TinyCircuits/TinyCircuits-TinyShield-Sensor-ASD2511/cad/TinyShield_SENSOR_BOARD_ASD2511_REV5-DETAILED_DRAWING_COMPACT-PNG.png

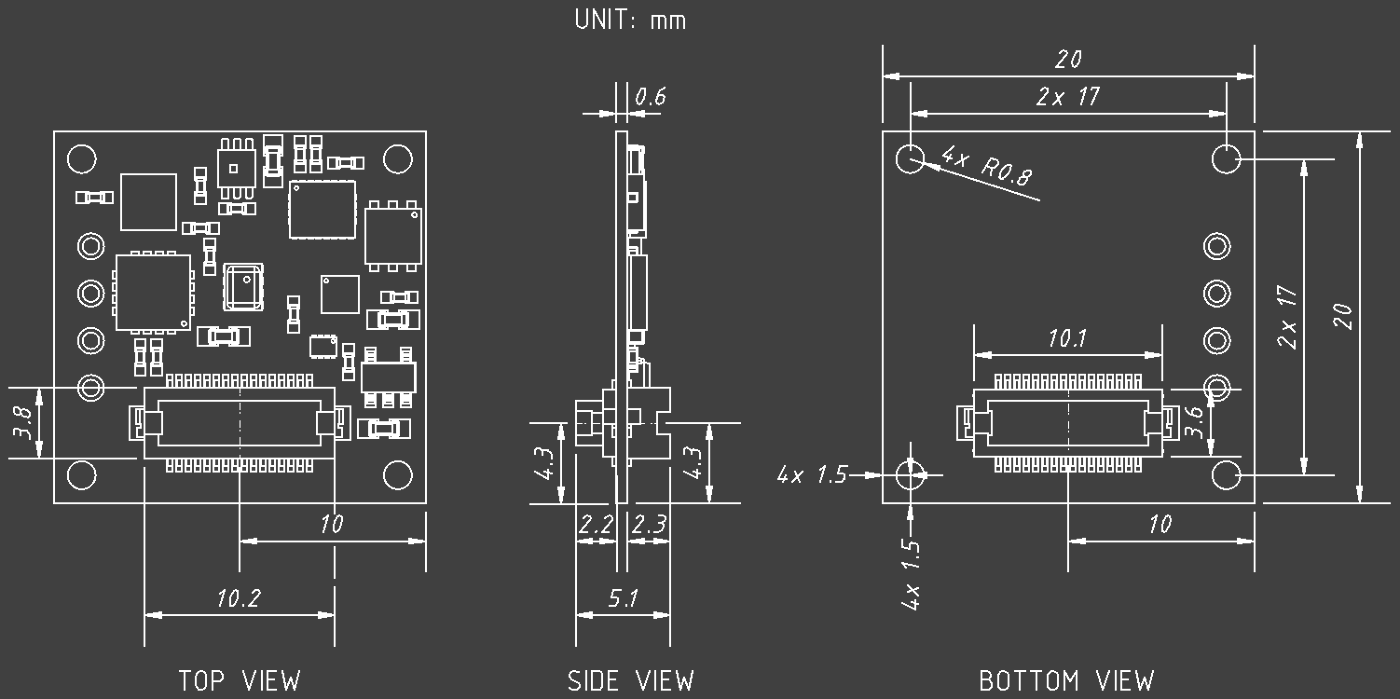
cad/TinyShield_SENSOR_BOARD_ASD2511_REV5-DETAILED_DRAWING_COMPACT-PNG.png
