TinyCircuits/TinyCircuits-TinyShield-Sensor-ASD2511/tutorial_images/ASD2511-R-P_Parts.JPG

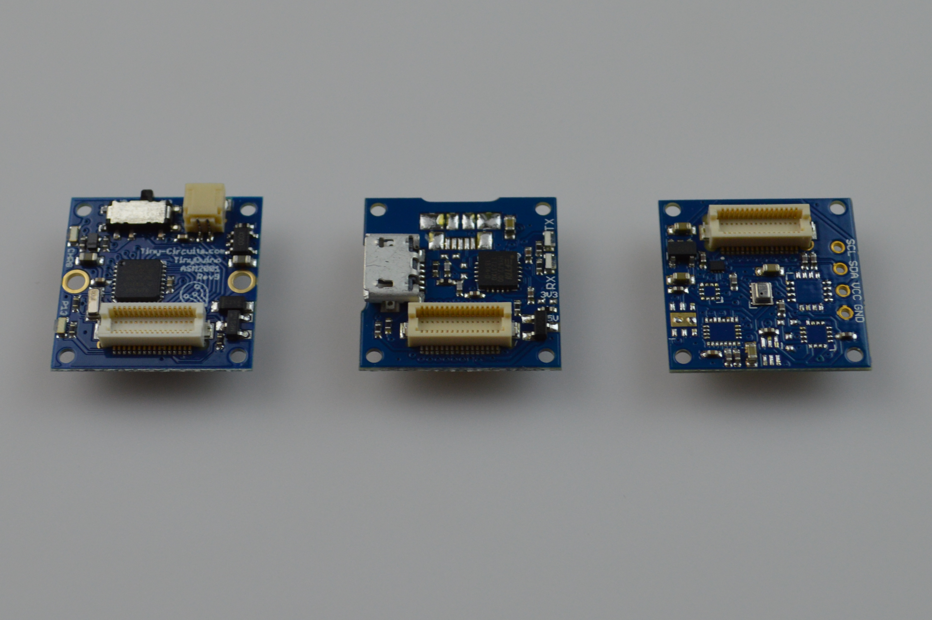
tutorial_images/ASD2511-R-P_Parts.JPG
