TinyCircuits/TinyCircuits-TinyShield-Sensor-ASD2511/images/tutorial_images_9-axis/ASD2511-R-N-Tutorial-Image-05.png

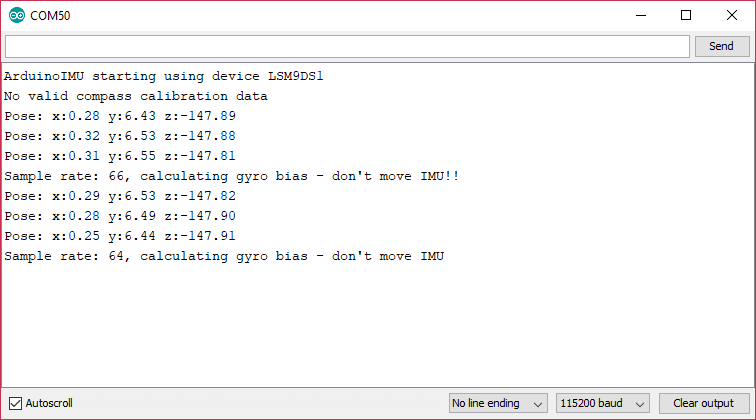
images/tutorial_images_9-axis/ASD2511-R-N-Tutorial-Image-05.png
