TinyCircuits/TinyCircuits-TinyShield-Sensor-ASD2511/images/tutorial_images_accelerometer/ASD2511-R-A-Tutorial-Image-03.jpg

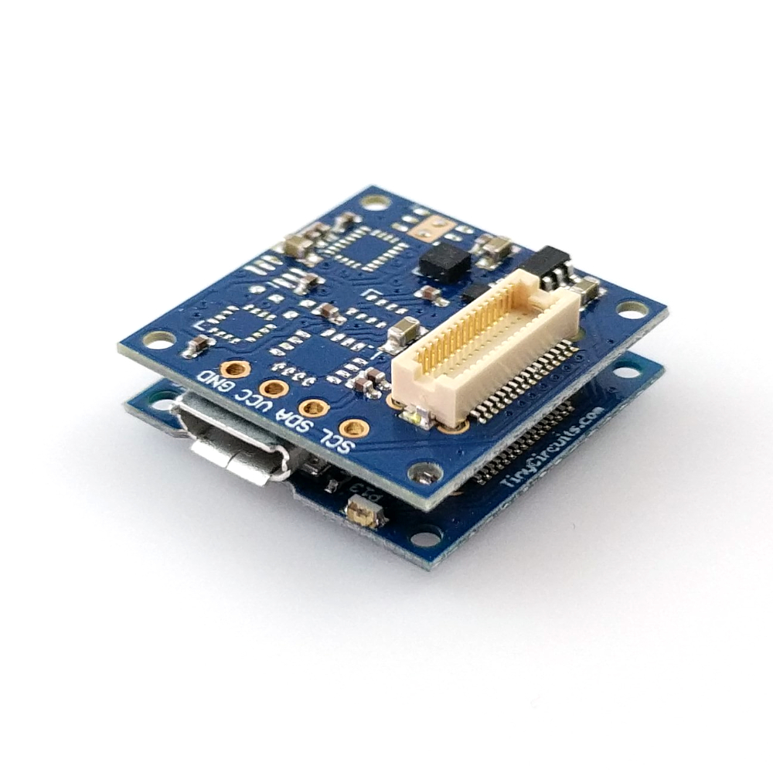
images/tutorial_images_accelerometer/ASD2511-R-A-Tutorial-Image-03.jpg
