TinyCircuits/TinyCircuits-TinyShield-Sensor-ASD2511/images/tutorial_images_accelerometer/ASD2511-R-A-Tutorial-Image-05.png

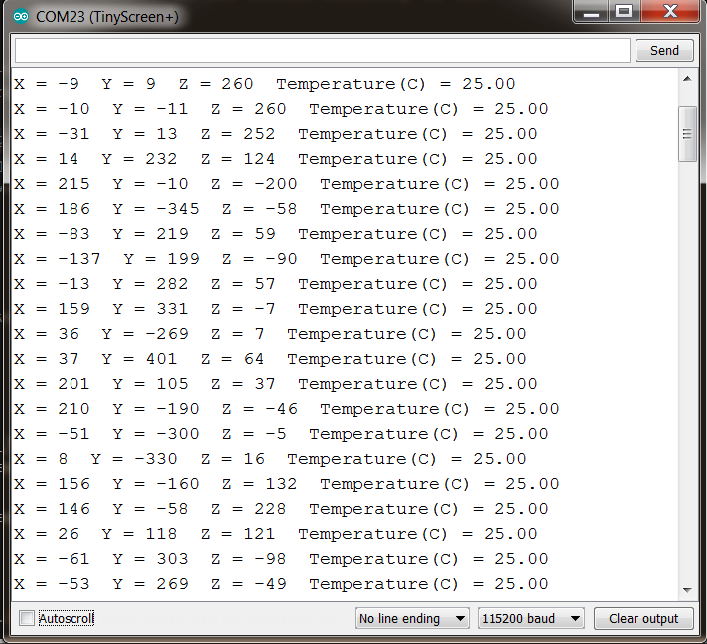
images/tutorial_images_accelerometer/ASD2511-R-A-Tutorial-Image-05.png
