TinyCircuits/TinyCircuits-TinyShield-Sensor-ASD2511/images/tutorial_images_barometric-pressure/ASD2511-R-P-Tutorial-Image-05.png

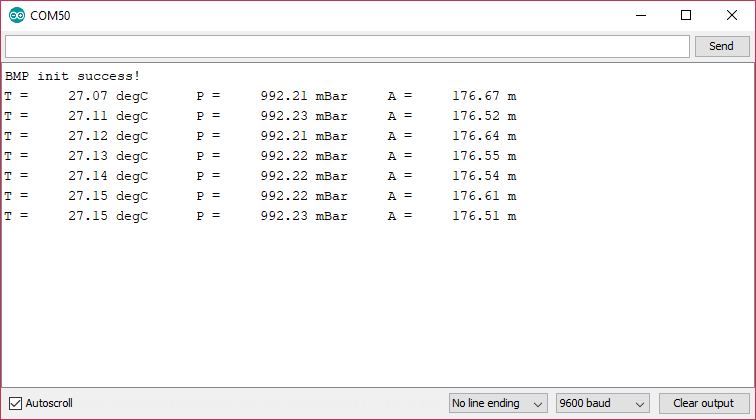
images/tutorial_images_barometric-pressure/ASD2511-R-P-Tutorial-Image-05.png
