TinyCircuits/TinyCircuits-TinyShield-Sensor-ASD2511/images/tutorial_images_combo/ASD2511-R-N-T-P-L-Tutorial-Image-02.jpg

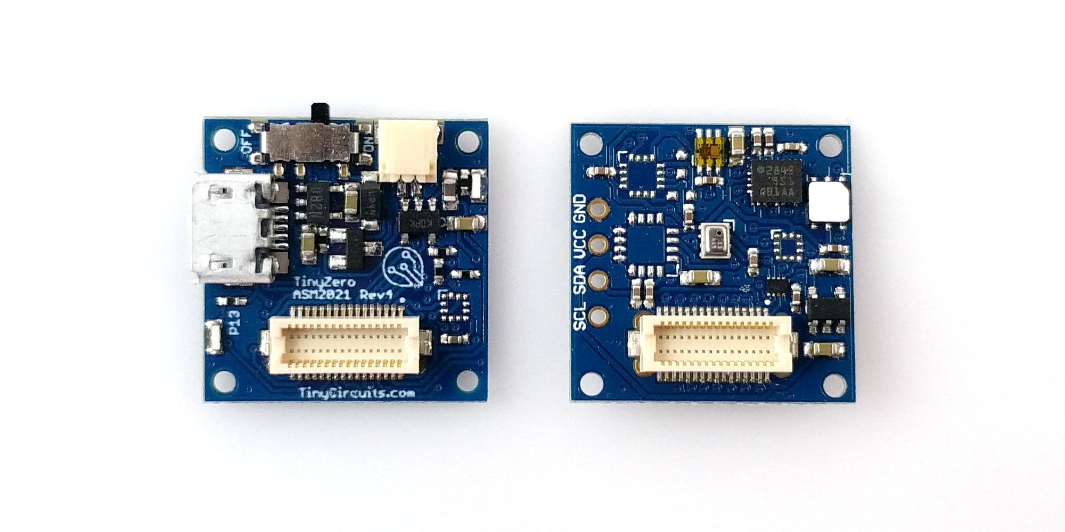
images/tutorial_images_combo/ASD2511-R-N-T-P-L-Tutorial-Image-02.jpg
