TinyCircuits/TinyCircuits-TinyShield-Sensor-ASD2511/images/tutorial_images_compass/ASD2511-R-C-Tutorial-Image-05.png

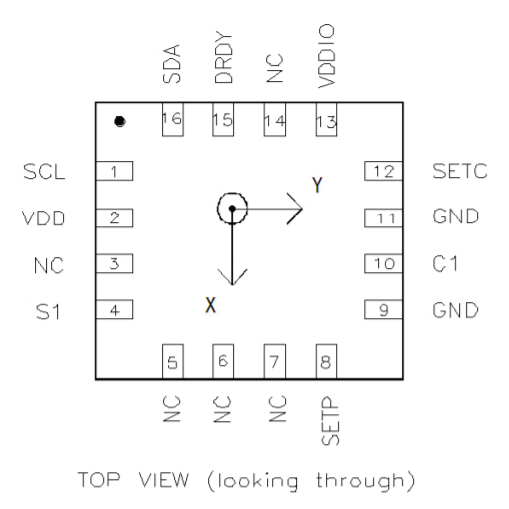
images/tutorial_images_compass/ASD2511-R-C-Tutorial-Image-05.png
