TinyCircuits/TinyCircuits-TinyShield-Sensor-ASD2511/images/tutorial_images_temperature-humidity/ASD2511-R-T-Tutorial-Image-01.png

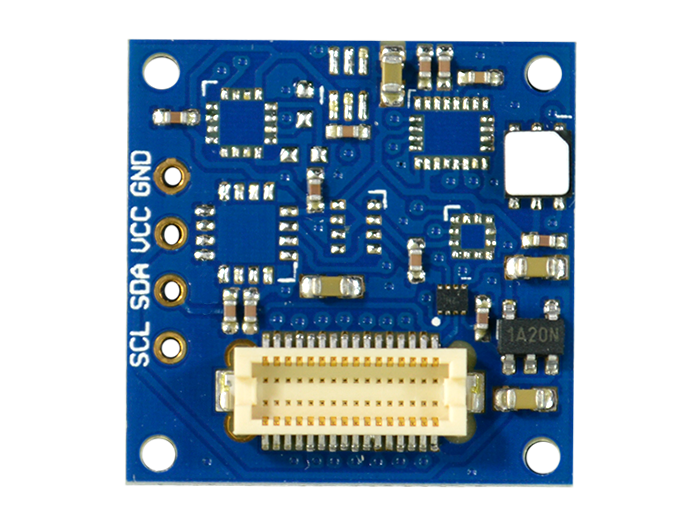
images/tutorial_images_temperature-humidity/ASD2511-R-T-Tutorial-Image-01.png
